Uspizig/SI4684-DAB-Receiver-Round/Images/IMG_20250820_204746.jpg

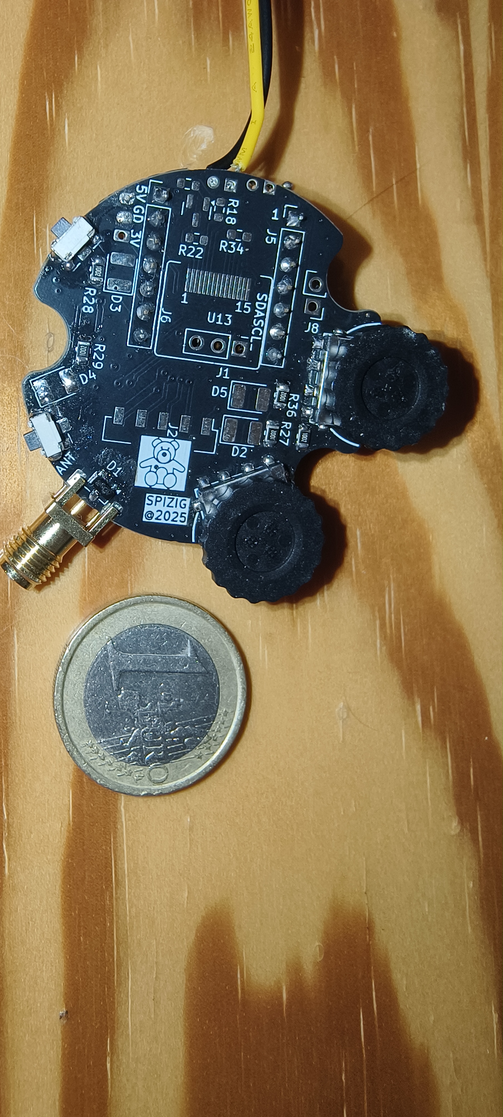
Images/IMG_20250820_204746.jpg
